manuel-rabade/receptor-alertas-same/prototipo/hardware/prototipo_receptor_same.sch

## EAGLE design prototipo/hardware/prototipo_receptor_same.sch (2023-10-05)

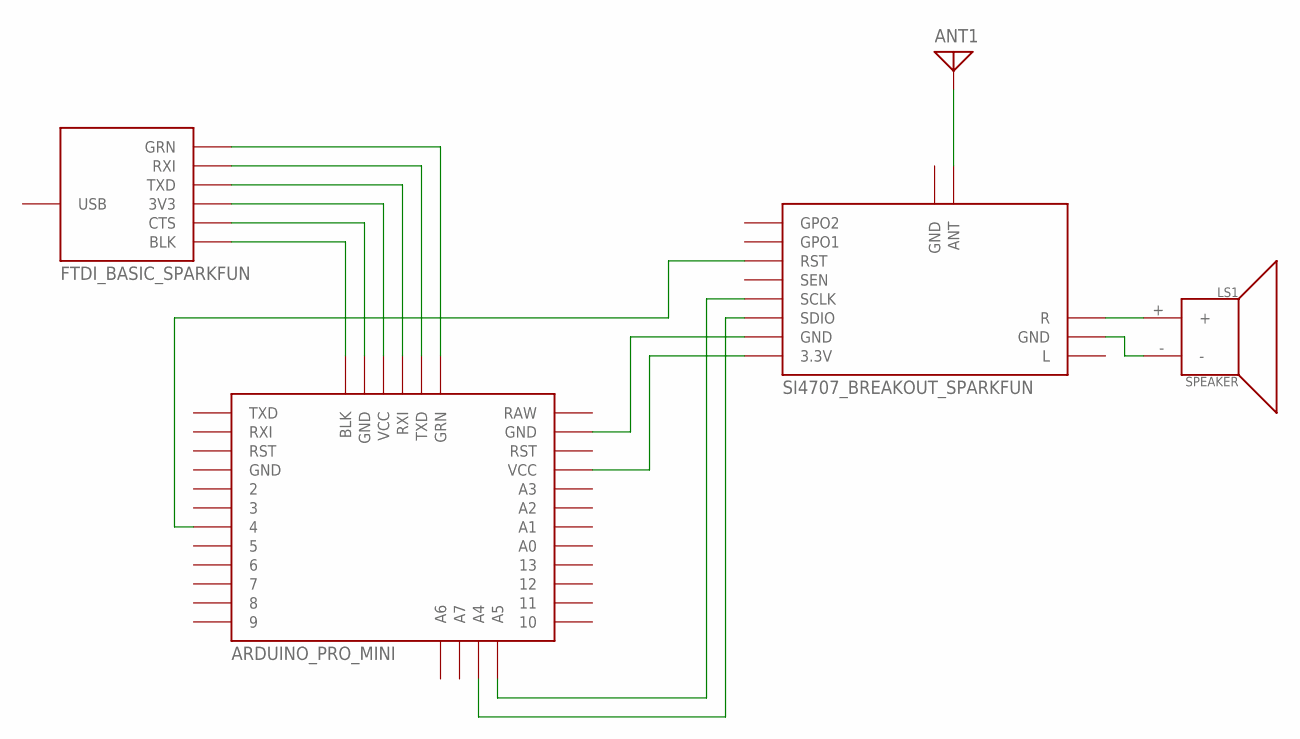
[picture p6: schematic prototipo_receptor_same.sch]

Parts:
ANT1: ANTENNA; PAD-01
LS1: SPEAKER; PCB_MOUNT_SPEAKER
